TrlRizu/TrlPad/screenshots/jlcpcb.png

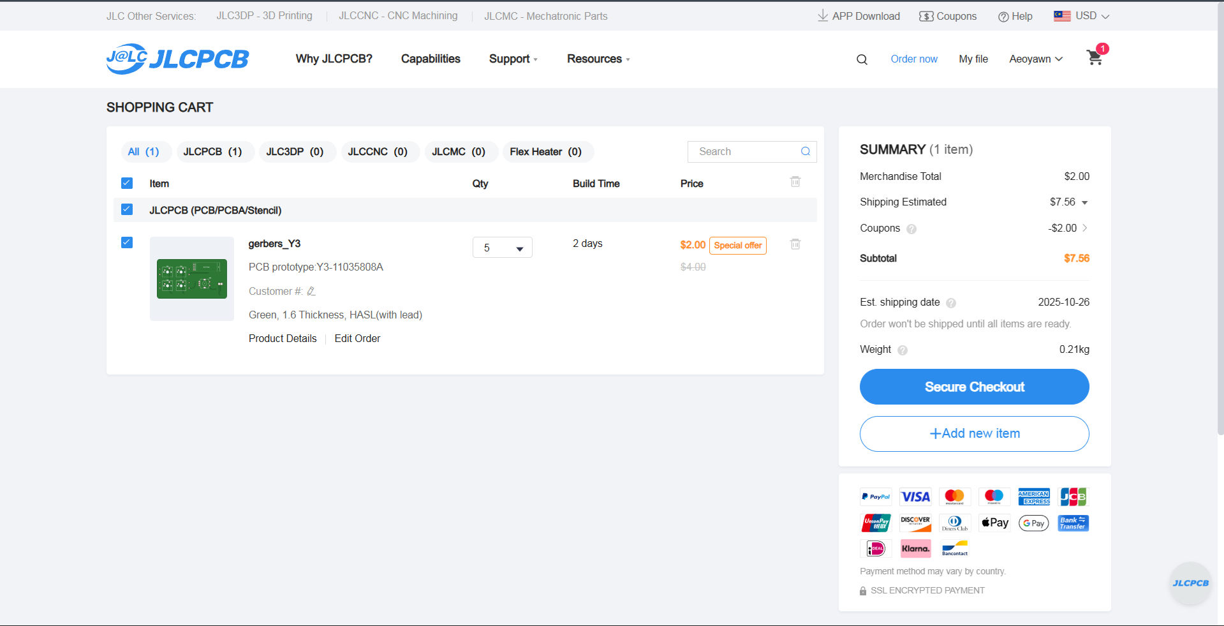
screenshots/jlcpcb.png
